KingVanilla/OpenHAB/Alarm Controller/Images/HABPanel installation.JPG

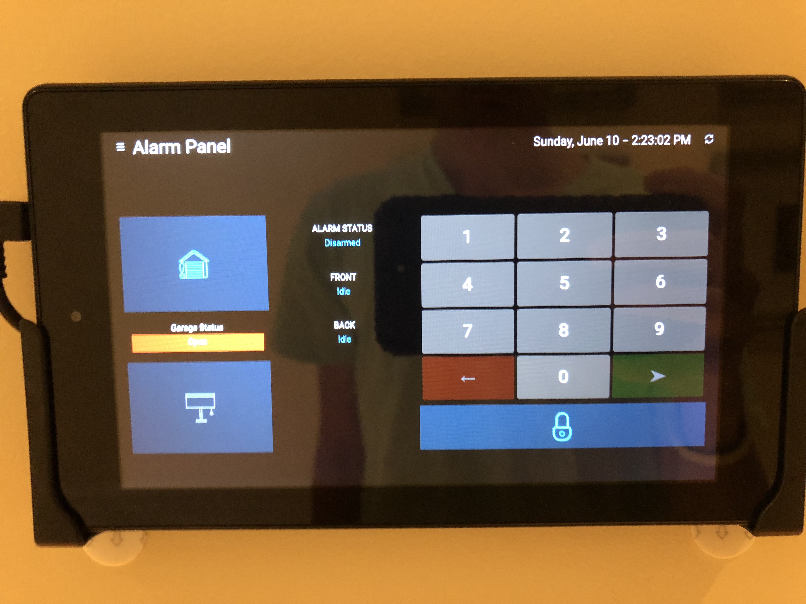
Alarm Controller/Images/HABPanel installation.JPG
